kesyog/hangman/hangman/src/weight/mod.rs

// Copyright 2023 Google LLC
//
// Licensed under the Apache License, Version 2.0 (the "License");
// you may not use this file except in compliance with the License.
// You may obtain a copy of the License at
//
//     https://www.apache.org/licenses/LICENSE-2.0
//
// Unless required by applicable law or agreed to in writing, software
// distributed under the License is distributed on an "AS IS" BASIS,
// WITHOUT WARRANTIES OR CONDITIONS OF ANY KIND, either express or implied.
// See the License for the specific language governing permissions and
// limitations under the License.

pub mod ads1230;
pub mod average;
mod calibrate;
pub mod hx711;
pub mod median;
mod random;
mod tare;
mod task;

extern crate alloc;

use crate::nonvolatile::Nvm;
pub use ads1230::Ads1230;
use alloc::boxed::Box;
use core::ops::DerefMut;
use embassy_sync::blocking_mutex::raw::RawMutex;
use embassy_sync::mutex::Mutex;
use embassy_time::{Duration, Instant};
pub use hx711::Hx711;
use once_cell::sync::OnceCell;
pub use task::task_function;

static SAMPLING_INTERVAL_HZ: OnceCell<usize> = OnceCell::new();
// Temporary defaults for test load cell
// TODO: provide better defaults for Hangman P1_0
pub const DEFAULT_CALIBRATION_M: f32 = 4.675_038e-6;
pub const DEFAULT_CALIBRATION_B: i32 = -100598;

type RawReading = i32;
pub type OnRawMeasurementCb = dyn FnMut(Duration, RawReading);
pub type OnCalibratedMeasurementCb = dyn FnMut(Duration, f32);
pub type OnTaredMeasurementCb = dyn FnMut(Duration, f32);

pub enum SampleType {
    Raw(Option<Box<OnRawMeasurementCb>>),
    FilteredRaw(Option<Box<OnRawMeasurementCb>>),
    Calibrated(Option<Box<OnCalibratedMeasurementCb>>),
    Tared(Option<Box<OnTaredMeasurementCb>>),
}

pub enum Command {
    /// Start measuring continuously
    StartSampling(SampleType),
    StopSampling,
    Tare,
    AddCalibrationPoint(f32),
    SaveCalibration,
}

impl defmt::Format for Command {
    fn format(&self, fmt: defmt::Formatter) {
        match self {
            Command::StartSampling(SampleType::Raw(_)) => defmt::write!(fmt, "StartSampling (Raw)"),
            Command::StartSampling(SampleType::FilteredRaw(_)) => {
                defmt::write!(fmt, "StartSampling (FilteredRaw)");
            }
            Command::StartSampling(SampleType::Calibrated(_)) => {
                defmt::write!(fmt, "StartSampling (Calibrated)");
            }
            Command::StartSampling(SampleType::Tared(_)) => {
                defmt::write!(fmt, "StartSampling (Tared)");
            }
            Command::StopSampling => defmt::write!(fmt, "StopSampling"),
            Command::Tare => defmt::write!(fmt, "Tare"),
            Command::AddCalibrationPoint(known_weight) => {
                defmt::write!(fmt, "AddCalibrationPoint: {=f32}", known_weight);
            }
            Command::SaveCalibration => defmt::write!(fmt, "SaveCalibration"),
        }
    }
}

pub struct Config {
    pub sampling_interval_hz: usize,
}

pub fn init(config: Config) {
    SAMPLING_INTERVAL_HZ
        .set(config.sampling_interval_hz)
        .expect("weight::init to be called only once");
}

pub fn sampling_interval_hz() -> usize {
    *SAMPLING_INTERVAL_HZ
        .get()
        .expect("weight::init to have been called")
}

async fn write_calibration(nvm: &mut Nvm, cal_m: f32, cal_b: RawReading) {
    nvm.write_cal_m(cal_m);
    nvm.write_cal_b(cal_b);
    nvm.flush().await;
}

pub struct Sample<T> {
    pub timestamp: Instant,
    pub value: T,
}

pub(crate) trait SampleProducerMut {
    type Output;

    async fn sample(&mut self) -> Sample<Self::Output>;
}

pub(crate) trait SampleProducer {
    type Output;

    async fn sample(&self) -> Sample<Self::Output>;
}

impl<T> SampleProducerMut for T
where
    T: SampleProducer,
{
    type Output = T::Output;

    async fn sample(&mut self) -> Sample<Self::Output> {
        SampleProducer::sample(self).await
    }
}

impl<T, M> SampleProducer for Mutex<M, T>
where
    T: SampleProducerMut,
    M: RawMutex,
{
    type Output = T::Output;

    async fn sample(&self) -> Sample<Self::Output> {
        let mut producer = self.lock().await;
        SampleProducerMut::sample(DerefMut::deref_mut(&mut producer)).await
    }
}

impl<T, M> SampleProducer for &Mutex<M, T>
where
    T: SampleProducerMut,
    M: RawMutex,
{
    type Output = T::Output;

    async fn sample(&self) -> Sample<<T as SampleProducerMut>::Output> {
        let mut producer = self.lock().await;
        SampleProducerMut::sample(DerefMut::deref_mut(&mut producer)).await
    }
}
