kesyog/hangman/hangman/src/lib.rs

// Copyright 2023 Google LLC
//
// Licensed under the Apache License, Version 2.0 (the "License");
// you may not use this file except in compliance with the License.
// You may obtain a copy of the License at
//
//     https://www.apache.org/licenses/LICENSE-2.0
//
// Unless required by applicable law or agreed to in writing, software
// distributed under the License is distributed on an "AS IS" BASIS,
// WITHOUT WARRANTIES OR CONDITIONS OF ANY KIND, either express or implied.
// See the License for the specific language governing permissions and
// limitations under the License.

#![cfg_attr(not(test), no_std)]
#![feature(type_alias_impl_trait)]
#![forbid(unsafe_op_in_unsafe_fn)]

pub mod battery_voltage;
pub mod ble;
pub mod button;
#[cfg(feature = "console")]
pub mod console;
pub mod nonvolatile;
pub mod sleep;
pub mod util;
pub mod weight;

use blocking_hal::Delay as SysTickDelay;
pub use embassy_nrf::pac;
use embassy_sync::{
    blocking_mutex::raw::NoopRawMutex,
    channel::{Channel, Receiver},
    mutex::Mutex,
};

#[cfg(feature = "nrf52832")]
pub use nrf52832_hal as blocking_hal;
#[cfg(feature = "nrf52840")]
pub use nrf52840_hal as blocking_hal;
use nrf_softdevice as _;
use panic_probe as _;

#[cfg(all(feature = "nrf52832", feature = "nrf52840"))]
compile_error!("features `nrf52832` and `nrf52840` are mutually exclusive");

#[cfg(all(not(feature = "nrf52832"), not(feature = "nrf52840")))]
compile_error!("one of `nrf52832` and `nrf52840` must be enabled");

pub type SharedDelay = Mutex<NoopRawMutex, SysTickDelay>;
pub type MeasureCommandChannel =
    Channel<NoopRawMutex, weight::Command, MEASURE_COMMAND_CHANNEL_SIZE>;
// Leave some room for multiple commands to be queued. If this is too small, we can get overwhelmed
// and deadlock.
pub const MEASURE_COMMAND_CHANNEL_SIZE: usize = 5;
pub type MeasureCommandReceiver =
    Receiver<'static, NoopRawMutex, weight::Command, MEASURE_COMMAND_CHANNEL_SIZE>;

/// Re-implementation of static_cell::make_static, which is broken on latest nightly
/// https://github.com/embassy-rs/static-cell/issues/16
#[macro_export]
macro_rules! make_static {
    ($t:ty, $val:expr) => ($crate::make_static!($t, $val,));
    ($t:ty, $val:expr, $(#[$m:meta])*) => {{
        $(#[$m])*
        static STATIC_CELL: static_cell::StaticCell<$t> = static_cell::StaticCell::new();
        STATIC_CELL.init_with(|| $val)
    }};
}
